s-grundner/HWEP-Sequencer/docu/Software_docs/Libs.png

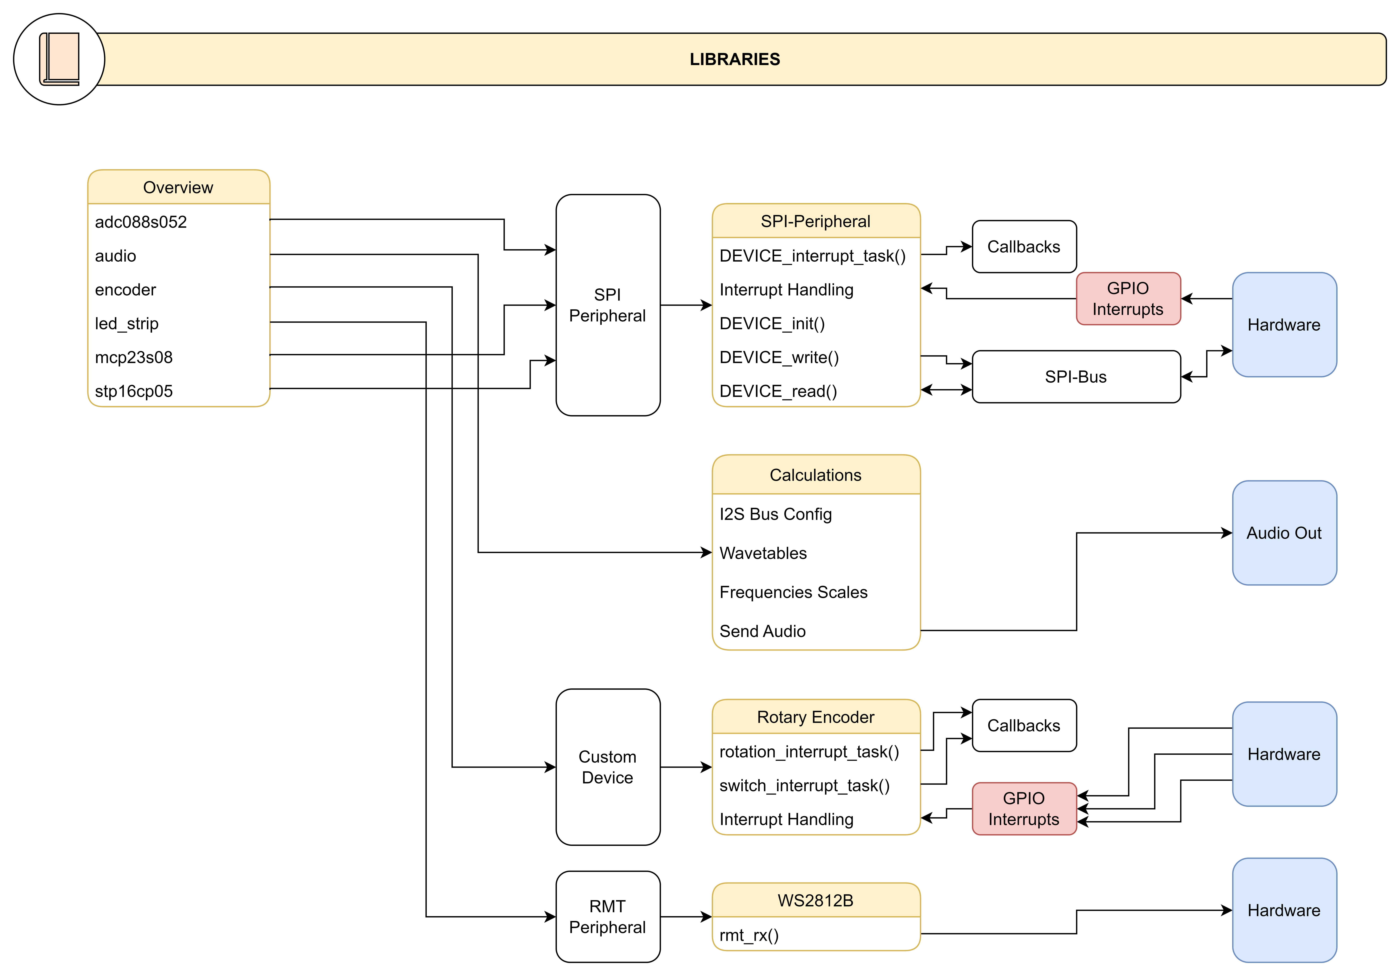
docu/Software_docs/Libs.png
