s-grundner/HWEP-Sequencer/manufacturing/hwep_sequencer_v2/docu/JLC-Order/images/Beilage-pcb-bot.png

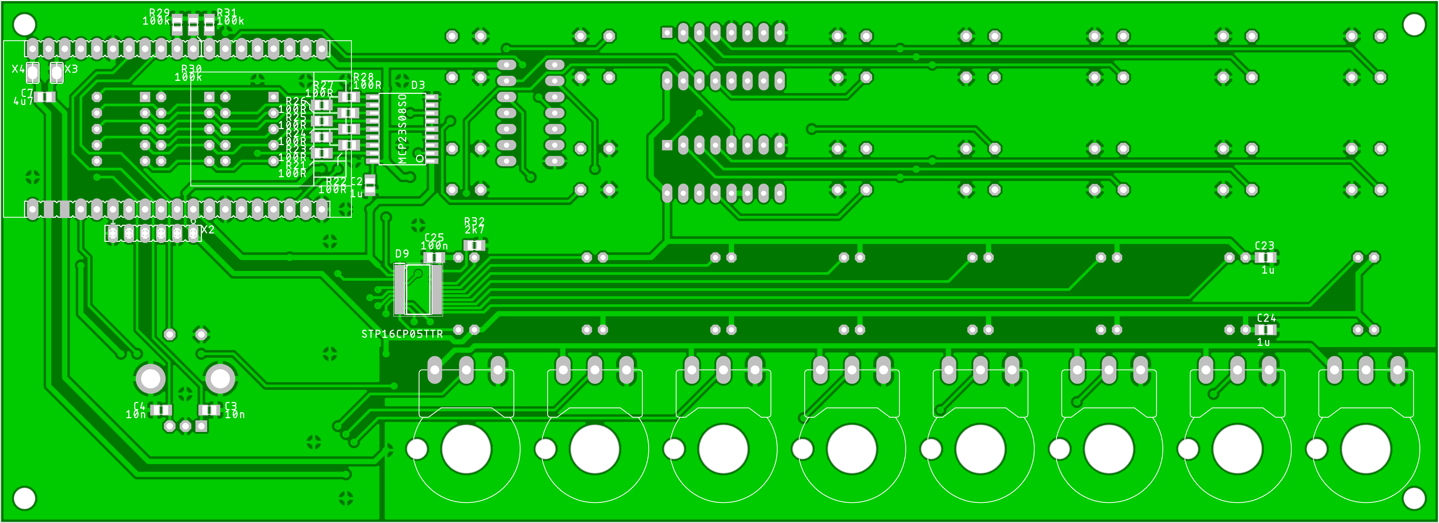
manufacturing/hwep_sequencer_v2/docu/JLC-Order/images/Beilage-pcb-bot.png
