s-grundner/HWEP-Sequencer/manufacturing/hwep_sequencer_v2/docu/JLC-Order/images/Beilage-stop-bottom.png

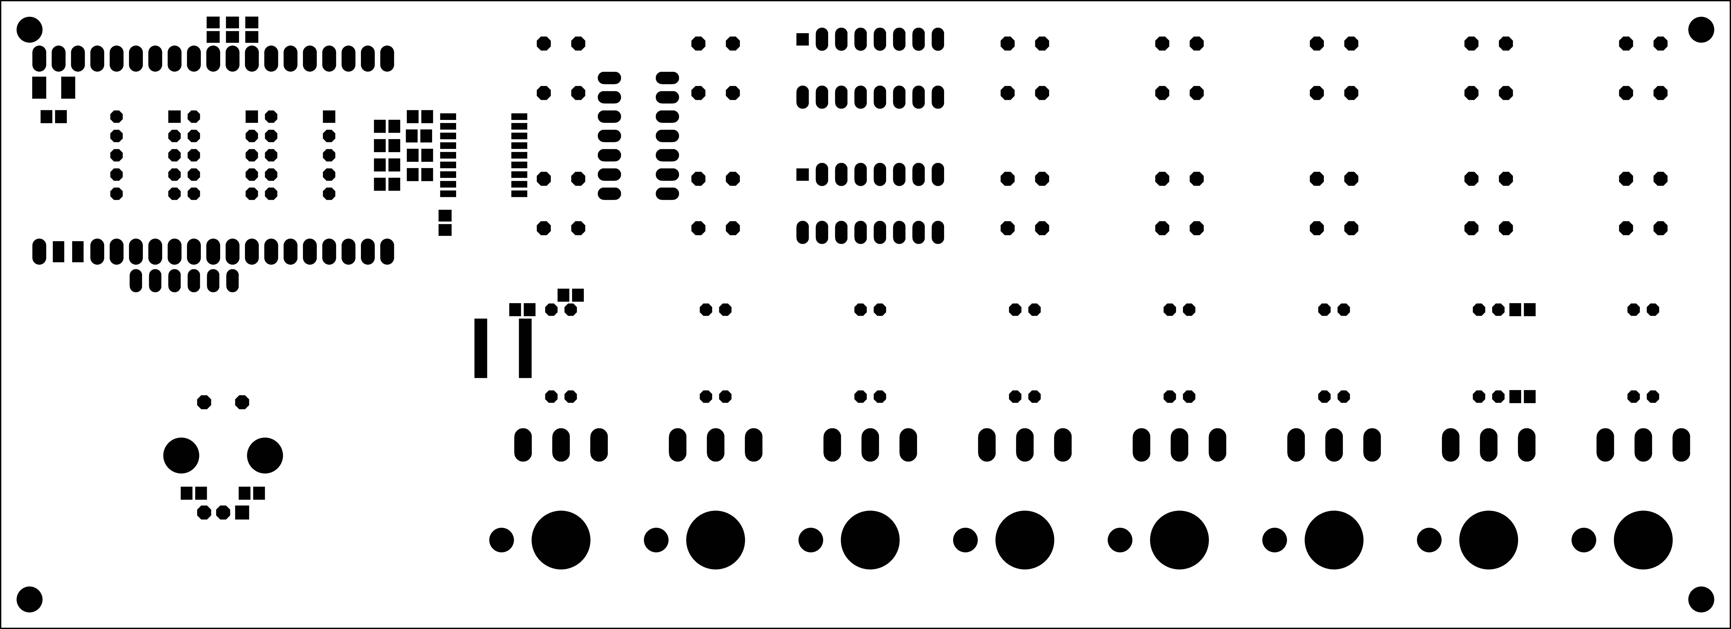
manufacturing/hwep_sequencer_v2/docu/JLC-Order/images/Beilage-stop-bottom.png
