s-grundner/HWEP-Sequencer/manufacturing/hwep_sequencer_v2/docu/2022-03-07/images/Beilage-construction.png

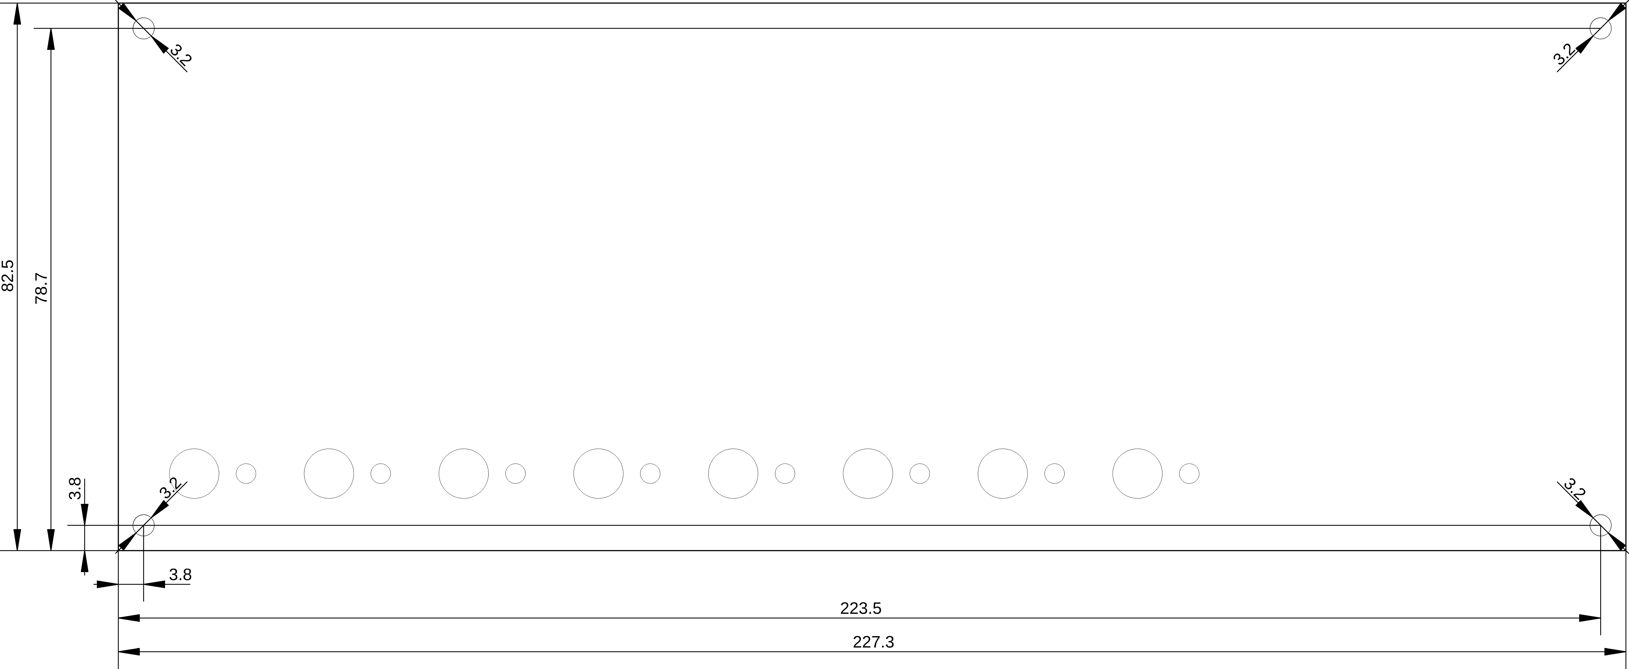
manufacturing/hwep_sequencer_v2/docu/2022-03-07/images/Beilage-construction.png
