s-grundner/HWEP-Sequencer/src/SRC_HWEP_Sequencer_V2/src/sequencer.c

#include "sequencer.h"
#include "esp_log.h"
static const gpio_num_t sseg_channel[3] = {GPIO_NUM_33, GPIO_NUM_25, GPIO_NUM_26};
static char app_mode_names[4][3] = {"BPM", "KEY", "ENR", "TSP"};
static const char *TAG = "sequencer header";

#define MUXTIME_US 5000
#define NEW_MODE_TIMEOUT_MS 2000
#define BTN_MASK_PAUSE (1 << 0)
#define BTN_MASK_RESET (1 << 1)
#define BTN_MASK_SHKEY (1 << 2)
#define BTN_MASK_SHIFT (1 << 3)
#define PRIO_BIT (1 << 3)

// ------------------------------------------------------------
// Timer Tasks
// ------------------------------------------------------------

SemaphoreHandle_t timer_sem;

QueueHandle_t refresh_q = NULL;
static void IRAM_ATTR refresh_isr(void *arg)
{
	sseg_context_t *ctx = (sseg_context_t *)arg;
	xQueueSendFromISR(refresh_q, &ctx, NULL);
}

static void IRAM_ATTR bpm_timer_task(TimerHandle_t bpm_timer)
{
	sequencer_handle_t ctx = (sequencer_handle_t)pvTimerGetTimerID(bpm_timer);
	if (!ctx->pause_flag)
		ctx->channel = (ctx->channel + 1) % ctx->reset_at_n;
}

// ------------------------------------------------------------
// Static functions and callbacks
// ------------------------------------------------------------

static void switch_cb(void *args)
{
	sequencer_handle_t ctx = (sequencer_handle_t)args;
	// ctx->encoder_positions[ctx->cur_appmode] = encoder_read(ctx->encoder_handle);

	ctx->cur_appmode = encoder_read_sw(ctx->encoder_handle);
	sseg_new_appmode(ctx);

	// encoder_write(ctx->encoder_handle, ctx->encoder_positions[ctx->cur_appmode]);
	ESP_LOGD(TAG, "Current mode%d", ctx->cur_appmode);
}

static void rot_cb(void *args)
{
	sequencer_handle_t sqc_handle = (sequencer_handle_t)args;
	sqc_handle->sseg_handle->sseg_refreshable = true;
}

static void mcp_cb(void *args)
{
	sequencer_handle_t sqc_handle = (sequencer_handle_t)args;
	if (xSemaphoreTake(timer_sem, 3) == pdTRUE)
	{
		uint8_t mcp_data;
		mcp23s08_read(sqc_handle->mcp_handle, IN_PS_HW_ADR, INTCAP, &mcp_data);
		uint8_t ps_data = mcp_data >> 4;
		uint8_t btn_data = ~mcp_data & 0x0f;

		// prescaler data
		if ((ps_data & PRIO_BIT) && (ps_data != 0x08))
		{
			sqc_handle->ps_bpm = (1 << ((ps_data & 0x7) - 3));
			ESP_LOGI(TAG, "ps: %02x", ps_data);
			update_bpm(sqc_handle);
		}
		else if (ps_data)
		{
			sqc_handle->ps_gate = (1 << (ps_data - 3));
		}
		sqc_handle->btn_shift = btn_data & BTN_MASK_SHIFT;
		sqc_handle->btn_reset = btn_data & BTN_MASK_RESET;
		sqc_handle->btn_shkey = btn_data & BTN_MASK_SHKEY;
		sqc_handle->btn_pause = btn_data & BTN_MASK_PAUSE;

		sqc_handle->shkey_flag ^= sqc_handle->btn_shkey;
		sqc_handle->pause_flag ^= sqc_handle->btn_pause;
		sqc_handle->osc.is_on = !sqc_handle->pause_flag;

		if (sqc_handle->btn_reset)
			sqc_handle->channel = 0;

		if (sqc_handle->btn_shift && (sqc_handle->cur_appmode == APP_MODE_ENR))
			sqc_handle->active_note_mask = sqc_handle->active_note_mask ^ get_pos_index(sqc_handle);

		xSemaphoreGive(timer_sem);
	}
}

#define SSEG_H (ctx->sseg_handle)
static void refresh_task(void *args)
{
	sequencer_handle_t ctx = (sequencer_handle_t)args;
	for (;;)
	{
		if (xQueueReceive(refresh_q, &ctx, portMAX_DELAY) == pdTRUE)
		{
			if (xSemaphoreTake(timer_sem, 3) == pdTRUE)
			{
				// Segment Multiplexing
				gpio_set_level(sseg_channel[SSEG_H->channel], 0);
				SSEG_H->channel = (SSEG_H->channel + 1) % SEG_CNT;
				mcp23s08_write(SSEG_H->mcp_handle, S_SEG_HW_ADR, GPIO_R, get_char_segment(SSEG_H->data_buffer[SSEG_H->channel]));
				gpio_set_level(sseg_channel[SSEG_H->channel], 1);

				// ADC reading
				ESP_ERROR_CHECK(adc088s052_get_raw(ctx->adc_handle, ctx->channel, &(ctx->cur_adc_data[ctx->channel])));

				// STP
				switch (ctx->cur_appmode)
				{
				case APP_MODE_BPM:
				case APP_MODE_KEY:
				case APP_MODE_TSP:
					ESP_ERROR_CHECK(stp_index(ctx));
					break;
				case APP_MODE_ENR:
					ESP_ERROR_CHECK(stp_cursor(ctx));
					break;
				default:
					break;
				}
				ctx->osc.is_on = (ctx->active_note_mask & (1 << ctx->channel)) ? 1 : 0;
				xSemaphoreGive(timer_sem);
			}
		}
	}
}

static void new_appmode(TimerHandle_t new_app_timer)
{
	sequencer_handle_t sqc_handle = (sequencer_handle_t)pvTimerGetTimerID(new_app_timer);
	sqc_handle->sseg_handle->sseg_refreshable = true;
}

// ------------------------------------------------------------
// Overall sequencer functions
// ------------------------------------------------------------

esp_err_t sequencer_init(sequencer_config_t **out_sqc_cfg)
{
	sequencer_config_t *sqc_cfg = (sequencer_config_t *)malloc(sizeof(sequencer_config_t));
	if (!sqc_cfg)
		return ESP_ERR_NO_MEM;

	// ------------------------------------------------------------
	// init Queues and create tasks
	// ------------------------------------------------------------
	vSemaphoreCreateBinary(timer_sem);
	refresh_q = xQueueCreate(10, sizeof(sequencer_handle_t));
	xTaskCreate(refresh_task, "sseg_mux_task", 2048, NULL, 10, NULL);

	// ------------------------------------------------------------
	// Audio
	// ------------------------------------------------------------
	i2s_init();
	ESP_ERROR_CHECK(init_wavetables());

	// ------------------------------------------------------------
	// SPI Bus
	// ------------------------------------------------------------
	spi_bus_config_t buscfg = {
		.max_transfer_sz = 32,
		.miso_io_num = VSPIQ,
		.mosi_io_num = VSPID,
		.sclk_io_num = VSCK,
	};
	ESP_ERROR_CHECK(spi_bus_initialize(VSPI, &buscfg, SPI_DMA_CH_AUTO));

	// ------------------------------------------------------------
	// Encoder
	// ------------------------------------------------------------
	encoder_handle_t encoder_handle;
	encoder_config_t ec_cfg = {
		.pin_a = A,
		.pin_b = B,
		.pin_sw = SW,
		.sw_max = MAX_APP_MODES - 1,
		.sw_callback = switch_cb,
		.sw_args = sqc_cfg,
		.rot_callback = rot_cb,
		.rot_args = sqc_cfg,
	};
	ESP_ERROR_CHECK(encoder_init(&encoder_handle, &ec_cfg));

	// ------------------------------------------------------------
	// Seven Segment Display and PS input Buttons (MCP23S08)
	// ------------------------------------------------------------
	mcp23s08_handle_t mcp_handle;
	mcp23s08_config_t mcp_cfg = {
		.cs_io = CS_MCP23S08,
		.host = VSPI,
		.miso_io = VSPIQ,
		.mosi_io = VSPID,
		.intr_io = MCP23S08_INTR,
		.mcp_callback = mcp_cb,
		.mcp_intr_args = sqc_cfg,
	};
	ESP_ERROR_CHECK(mcp23s08_init(&mcp_handle, &mcp_cfg));
	ESP_ERROR_CHECK(mcp23s08_write(mcp_handle, 0, IOCON, (1 << HAEN) | (1 << INTPOL))); // Enable multiple MCP for same spi transaction
	ESP_ERROR_CHECK(mcp23s08_write(mcp_handle, S_SEG_HW_ADR, IODIR, 0x00));				// Set display MCP-GPIO as Output
	ESP_ERROR_CHECK(mcp23s08_write(mcp_handle, IN_PS_HW_ADR, IODIR, 0xff));				// Set Button MCP-GPIO as Input (Default as Input)
	ESP_ERROR_CHECK(mcp23s08_write(mcp_handle, IN_PS_HW_ADR, GPPU, 0x0f));				// Enable Internal Pullups for Buttons (not prio buttons)

	// Interrupt Settings for Input MCP
	ESP_ERROR_CHECK(mcp23s08_write(mcp_handle, IN_PS_HW_ADR, DEFVAL, 0x0f)); // Set default values
	ESP_ERROR_CHECK(mcp23s08_write(mcp_handle, IN_PS_HW_ADR, INTCON, 0x00)); // Interrupt on change

	ESP_ERROR_CHECK(mcp23s08_write(mcp_handle, IN_PS_HW_ADR, GPINTEN, 0xff)); // Enables Interrupts for all GPI
	ESP_ERROR_CHECK(mcp23s08_dump_intr(mcp_handle, IN_PS_HW_ADR));

	// ----------------------------------------------------------
	// STP LED Driver
	// ------------------------------------------------------------
	stp16cp05_handle_t stp_handle;
	stp16cp05_config_t stp_cfg = {
		.cs_io = CS_STP16CP05,
		.host = VSPI,
		.miso_io = VSPIQ,
		.mosi_io = VSPID,
	};
	ESP_ERROR_CHECK(stp16cp05_init(&stp_handle, &stp_cfg));

	// ------------------------------------------------------------
	// Seven Segment Display and PS input Buttons (MCP23S08)
	// ------------------------------------------------------------
	sseg_handle_t sseg_handle;
	sseg_init(&sseg_handle, sqc_cfg);

	// ------------------------------------------------------------
	// ADC
	// ------------------------------------------------------------
	adc088s052_handle_t adc_handle;
	adc088s052_config_t adc_cfg = {
		.cs_io = CS_ADC0880S052,
		.host = VSPI,
		.miso_io = VSPIQ,
		.mosi_io = VSPID,
	};
	ESP_ERROR_CHECK(adc088s052_init(&adc_handle, &adc_cfg));

	// ------------------------------------------------------------
	// BPM Cycle Timer
	// ------------------------------------------------------------
	TimerHandle_t bpm_timer = xTimerCreate(
		"bpm_timer",
		(bpm_to_ms(START_BPM) / portTICK_PERIOD_MS),
		pdTRUE,
		sqc_cfg,
		bpm_timer_task);
	xTimerStart(bpm_timer, 2);

	// ------------------------------------------------------------
	// Default Assignments
	// ------------------------------------------------------------
	*sqc_cfg = (sequencer_config_t){
		.adc_handle = adc_handle,
		.encoder_handle = encoder_handle,
		.stp_handle = stp_handle,
		.mcp_handle = mcp_handle,
		.sseg_handle = sseg_handle,
		.bpm_timer = bpm_timer,

		.channel = 0,
		.cur_appmode = APP_MODE_BPM,
		.cur_bpm = START_BPM,

		.osc = {
			.wavetable = get_wavetable(SINE_WT),
			.pitch = get_pitch_hz(40),
			.sample_pos = 0,
			.oct_offset = 0,
		},

		.encoder_positions[APP_MODE_ENR] = 2 * (ADC0880S052_CHANNEL_MAX - 1),
		.reset_at_n = ADC0880S052_CHANNEL_MAX,
		.active_note_mask = 0xff,

		.ps_bpm = 1,
		.ps_gate = 1,
	};

	// ------------------------------------------------------------
	// Store data in the out-handle
	// ------------------------------------------------------------
	*out_sqc_cfg = sqc_cfg;
	return ESP_OK;
}

// ------------------------------------------------------------
// LED row (upper and lower) specific functions
// ------------------------------------------------------------

esp_err_t stp_index(sequencer_handle_t sqc_handle)
{
	return stp16cp05_write(
		sqc_handle->stp_handle,
		sqc_handle->active_note_mask,
		1 << sqc_handle->channel);
}

esp_err_t stp_cursor(sequencer_handle_t sqc_handle)
{
	return stp16cp05_write(
		sqc_handle->stp_handle,
		sqc_handle->active_note_mask,
		get_pos_index(sqc_handle));
}

// ------------------------------------------------------------
// Seven Segment functions
// ------------------------------------------------------------

esp_err_t sseg_init(sseg_context_t **out_sseg_ctx, sequencer_handle_t sqc_handle)
{
	sseg_context_t *sseg_ctx = (sseg_context_t *)malloc(sizeof(sseg_context_t));
	if (sseg_ctx == NULL)
		return ESP_ERR_NO_MEM;

	gpio_config_t cf = {
		.mode = GPIO_MODE_OUTPUT,
		.pin_bit_mask = S_SEG_CHANNEL_MASK,
	};
	gpio_config(&cf);

	gpio_set_level(SEG_CH_E, 1);
	gpio_set_level(SEG_CH_Z, 1);
	gpio_set_level(SEG_CH_H, 1);

	TimerHandle_t new_mode_timer = xTimerCreate(
		"new_app_timer",
		NEW_MODE_TIMEOUT_MS / portTICK_PERIOD_MS,
		pdFALSE,
		sqc_handle,
		new_appmode);

	esp_timer_handle_t timer_handle;
	esp_timer_create_args_t timer_cfg = {
		.name = "mux",
		.callback = &refresh_isr,
		.arg = sqc_handle,
	};
	ESP_ERROR_CHECK(esp_timer_create(&timer_cfg, &timer_handle));

	*sseg_ctx = (sseg_context_t){
		.channel = 0,
		.data_buffer = malloc(sizeof(uint8_t) * SEG_CNT),
		.mcp_handle = sqc_handle->mcp_handle,
		.mux_timer = timer_handle,
		.new_mode_timer = new_mode_timer,
	};
	if (sseg_ctx->data_buffer == NULL)
	{
		free(sseg_ctx);
		return ESP_ERR_NO_MEM;
	}
	sseg_ctx->data_buffer = "BPM";
	xTimerStart(new_mode_timer, 0);

	ESP_ERROR_CHECK(esp_timer_start_periodic(sseg_ctx->mux_timer, MUXTIME_US));
	*out_sseg_ctx = sseg_ctx;
	return ESP_OK;
}

esp_err_t sseg_write(sseg_context_t *sseg_handle, char *data)
{
	if (strcmp(sseg_handle->data_buffer, data))
	{
		ESP_ERROR_CHECK(esp_timer_stop(sseg_handle->mux_timer));
		sseg_handle->data_buffer = data;
		ESP_ERROR_CHECK(esp_timer_start_periodic(sseg_handle->mux_timer, MUXTIME_US));
	}
	return ESP_OK;
}

esp_err_t sseg_new_appmode(sequencer_handle_t sqc_handle)
{
	// start newmode init on segment display
	sseg_write(sqc_handle->sseg_handle, app_mode_names[sqc_handle->cur_appmode]);
	sqc_handle->sseg_handle->sseg_refreshable = false;
	xTimerStartFromISR(sqc_handle->sseg_handle->new_mode_timer, pdFALSE);
	return ESP_OK;
}

// ------------------------------------------------------------
// MISC functions
// ------------------------------------------------------------

uint8_t get_pos_index(sequencer_handle_t sqc_handle)
{
	return 1 << abs(sqc_handle->encoder_positions[sqc_handle->cur_appmode] >> 1) % ADC0880S052_CHANNEL_MAX;
}

uint32_t bpm_to_us(uint16_t bpm)
{
	return 0x3938700 / (bpm ? bpm : START_BPM);
}

uint32_t bpm_to_ms(uint16_t bpm)
{
	return 0xea60 / (bpm ? bpm : START_BPM);
}

void update_bpm(sequencer_handle_t sqc_handle)
{
	sqc_handle->cur_bpm = START_BPM + sqc_handle->encoder_positions[sqc_handle->cur_appmode];
	xTimerChangePeriod(sqc_handle->bpm_timer, pdMS_TO_TICKS(bpm_to_ms(sqc_handle->cur_bpm * sqc_handle->ps_bpm)), 2);
}

// ------------------------------------------------------------
// Manager functions
// ------------------------------------------------------------

void manage_display(sequencer_handle_t sqc_handle)
{
	if (sqc_handle->sseg_handle->sseg_refreshable)
	{
		if (sqc_handle->shkey_flag)
		{
			sseg_write(sqc_handle->sseg_handle, get_key_name(get_key_num(sqc_handle->osc.pitch)));
		}
		else
		{
			char str[] = "   ";
			switch (sqc_handle->cur_appmode)
			{
			case APP_MODE_BPM:
				// write display data
				sseg_write(sqc_handle->sseg_handle, sqc_handle->btn_shift ? get_wt_name(sqc_handle->osc.wt_index) : itoa(sqc_handle->cur_bpm, str, 10));
				break;
			case APP_MODE_KEY:
				// write display data
				sseg_write(sqc_handle->sseg_handle, sqc_handle->btn_shift ? get_modal_name(sqc_handle->cur_modal) : get_key_name(sqc_handle->cur_key));
				break;
			case APP_MODE_ENR:
				break;
			case APP_MODE_TSP:
				// write display data
				sseg_write(sqc_handle->sseg_handle, sqc_handle->btn_shift ? itoa(sqc_handle->osc.oct_offset, str, 10) : itoa(sqc_handle->osc.transpose, str, 10));
				break;
			default:
				break;
			}
		}
	}
}

#define OSC (sqc_handle->osc)
void manage_audio(sequencer_handle_t sqc_handle)
{
	OSC.pitch = get_pitch_hz(adc_to_num(sqc_handle->cur_adc_data[sqc_handle->channel], OSC.oct_offset) + (OSC.transpose));
	send_audio_stereo(&sqc_handle->osc);
}

// manage ws2812
// manage sseg
